Mister-Industries/tinyCore/assets/Photos/image2.png

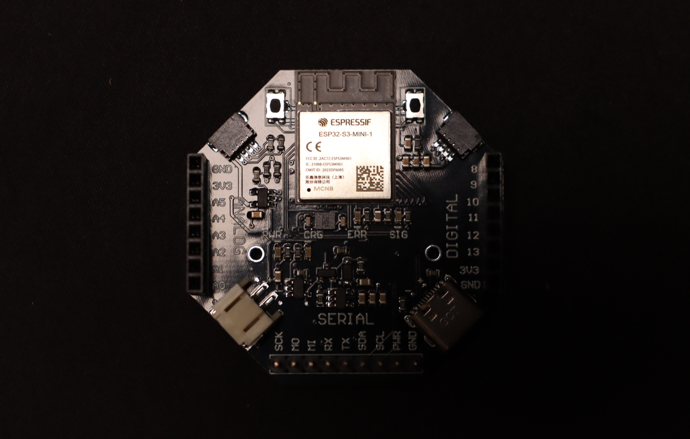
assets/Photos/image2.png
