Mister-Industries/tinyCore/assets/Photos/image5.png

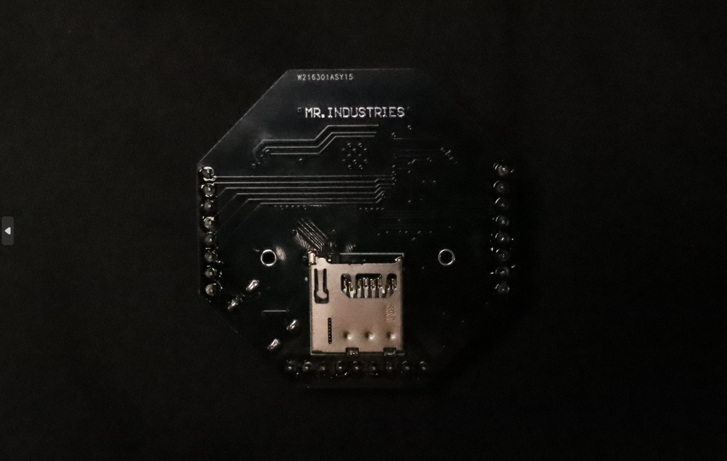
assets/Photos/image5.png
