Mister-Industries/tinyCore/assets/Photos/image6.png

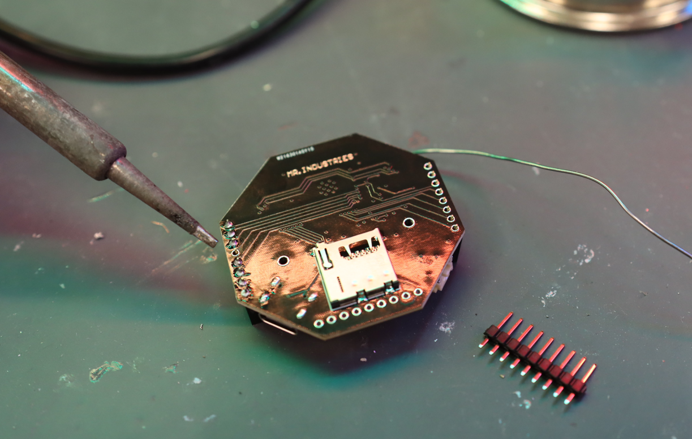
assets/Photos/image6.png
