Mister-Industries/tinyCore/assets/Photos/image7.png

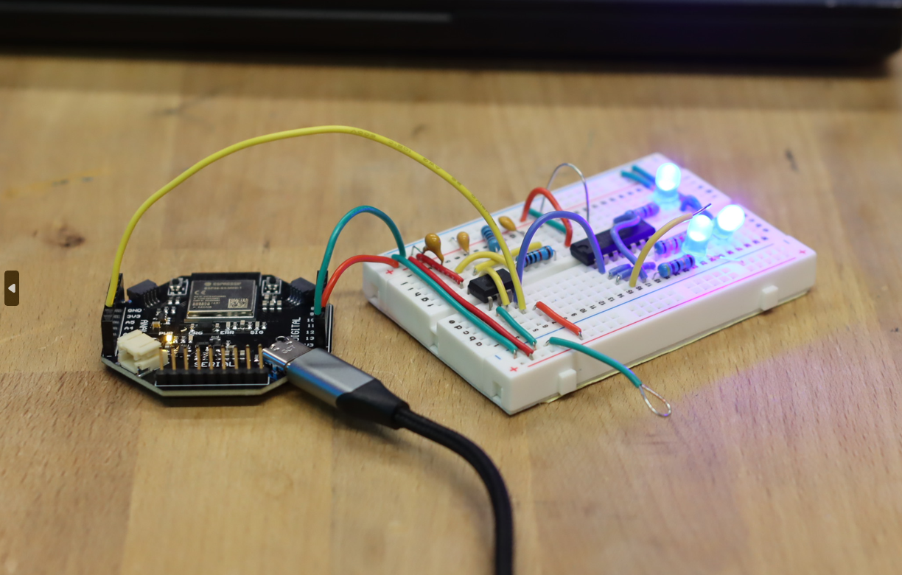
assets/Photos/image7.png
