Mister-Industries/tinyCore/assets/Photos/image9.png

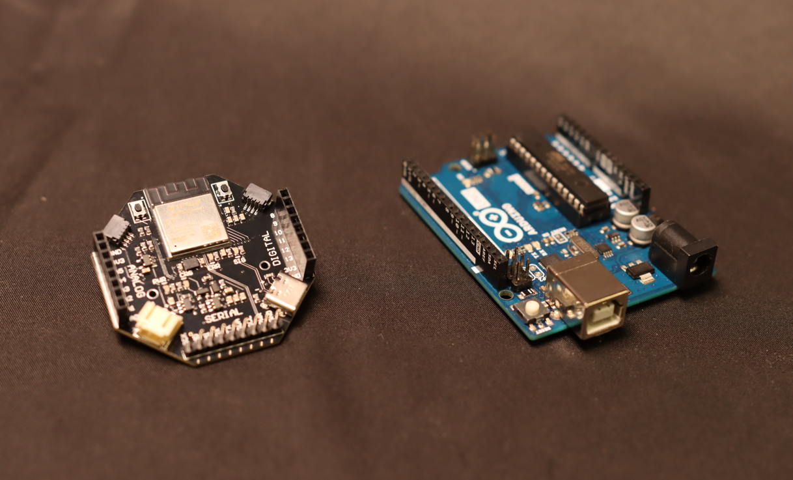
assets/Photos/image9.png
