Mister-Industries/tinyCore/assets/Photos/tinyCore-4Colors.png

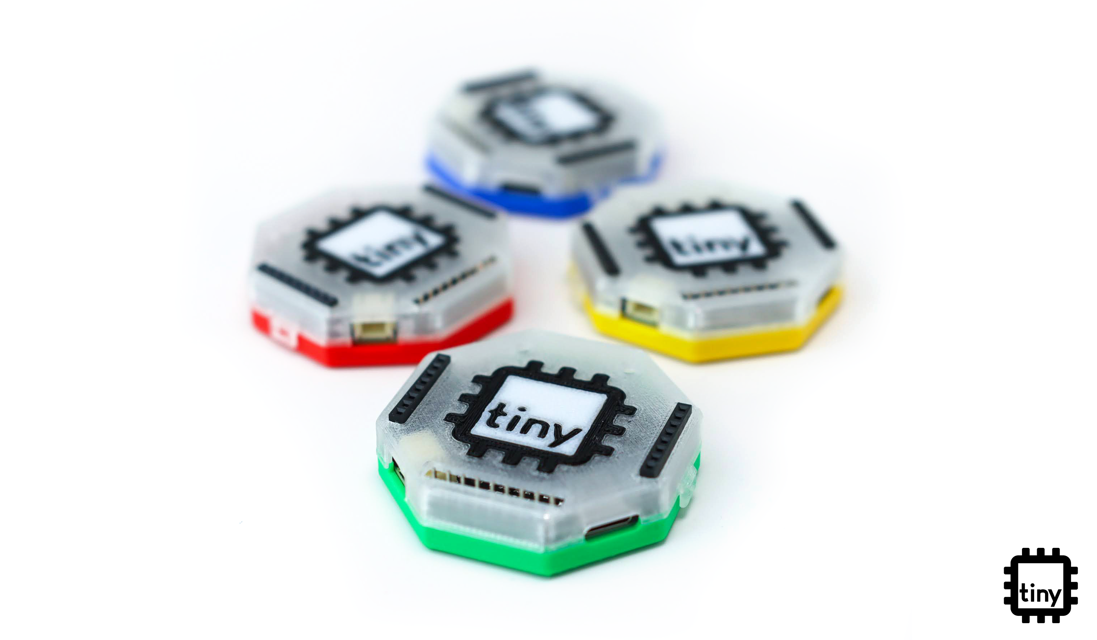
assets/Photos/tinyCore-4Colors.png
