Mister-Industries/tinyCore/assets/Photos/tinyCore-store-2.jpg

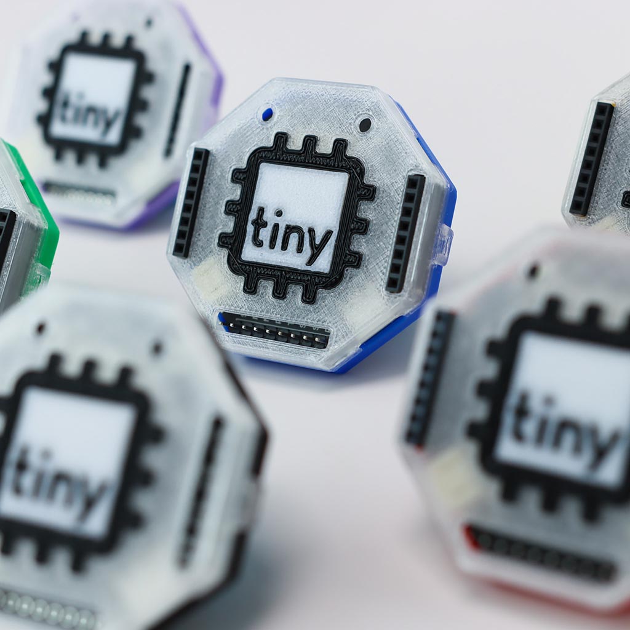
assets/Photos/tinyCore-store-2.jpg
