Mister-Industries/tinyCore/assets/Photos/tinyCore-store-3.jpg

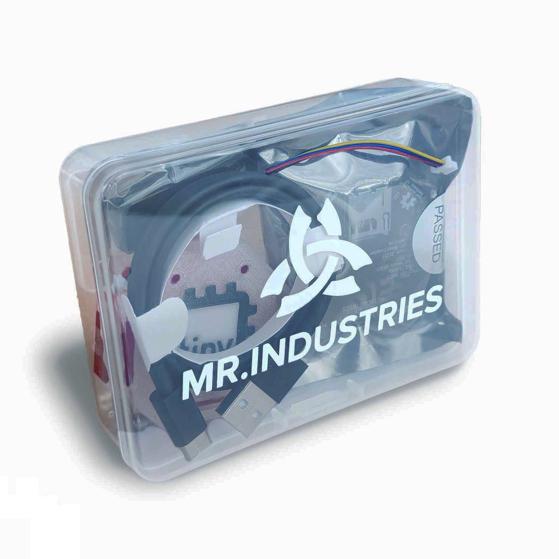
assets/Photos/tinyCore-store-3.jpg
