Mister-Industries/tinyCore/assets/Photos/tinyCore-store-3.png

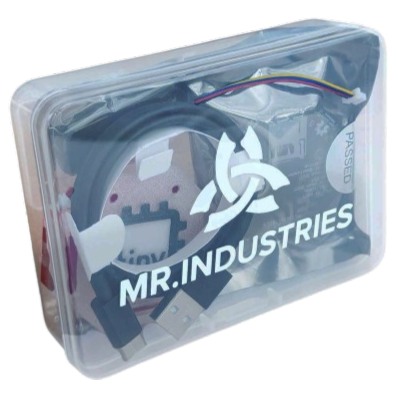
assets/Photos/tinyCore-store-3.png
