Mister-Industries/tinyCore/assets/Photos/tinyCore-store-4.jpg

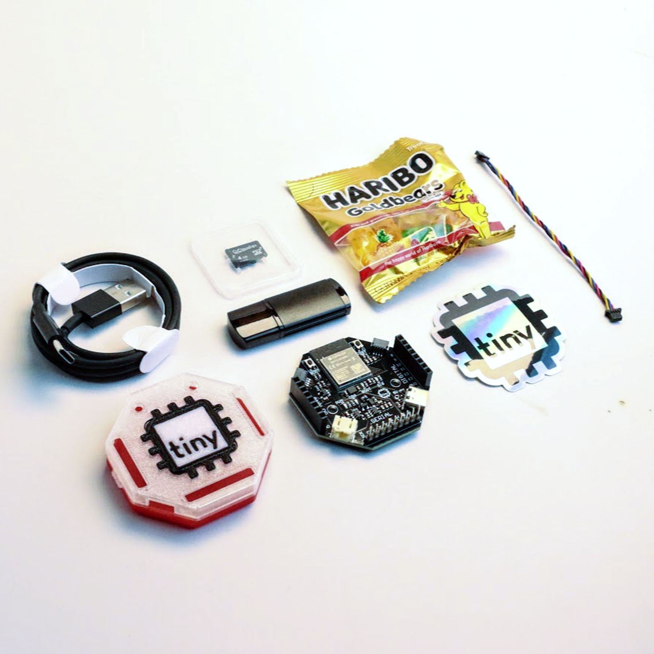
assets/Photos/tinyCore-store-4.jpg
