Mister-Industries/tinyCore/assets/Photos/tinyCore-store-5.jpg

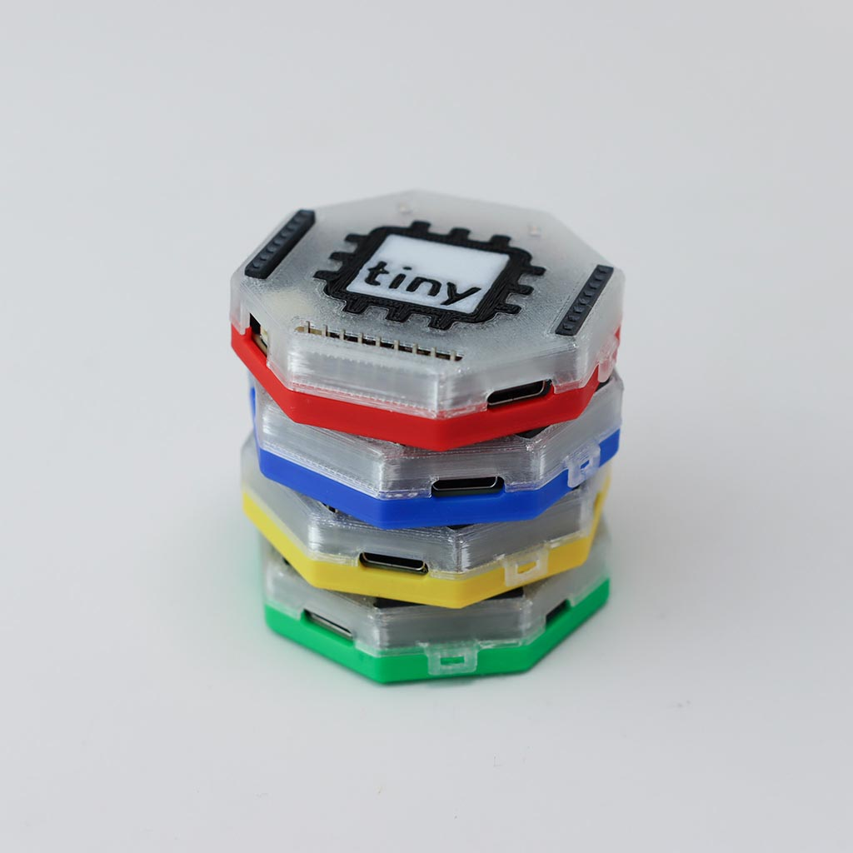
assets/Photos/tinyCore-store-5.jpg
