Mister-Industries/tinyCore/assets/Renders/Backside.png

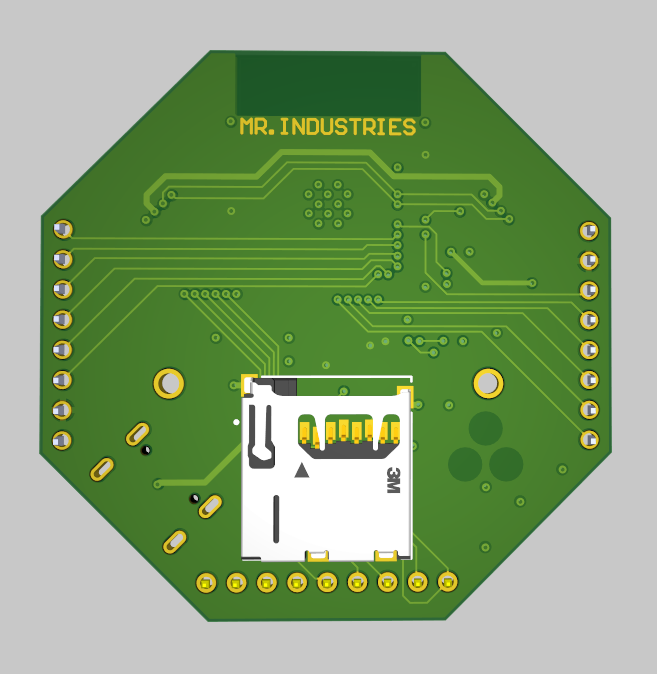
assets/Renders/Backside.png
