Mister-Industries/tinyCore/assets/Renders/IotaCoreRender.png

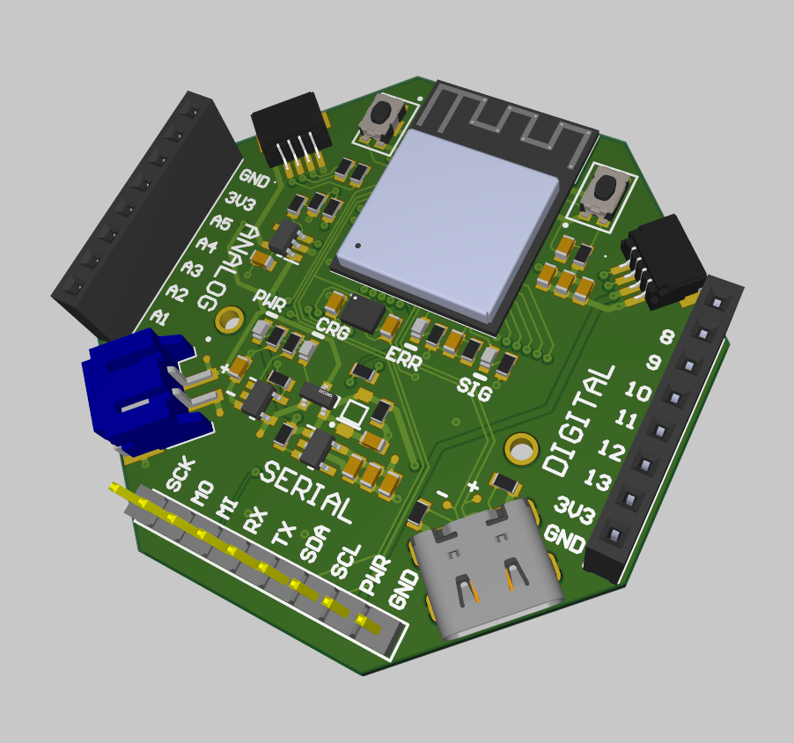
assets/Renders/IotaCoreRender.png
