Mister-Industries/tinyCore/Software/Arduino/Examples/ESP-NOW/ESP_NOW_Serial_AP/ESP_NOW_Serial_AP.ino

/*
    ESP-NOW Serial Example - Unicast transmission
    Lucas Saavedra Vaz - 2024
    Send data between two ESP32s using the ESP-NOW protocol in one-to-one (unicast) configuration.
    Note that different MAC addresses are used for different interfaces.
    The devices can be in different modes (AP or Station) and still communicate using ESP-NOW.
    The only requirement is that the devices are on the same Wi-Fi channel.
    Set the peer MAC address according to the device that will receive the data.

    Example setup:
    - Device 1: AP mode with MAC address F6:12:FA:42:B6:E8
                Peer MAC address set to the Station MAC address of Device 2 (F4:12:FA:40:64:4C)
    - Device 2: Station mode with MAC address F4:12:FA:40:64:4C
                Peer MAC address set to the AP MAC address of Device 1 (F6:12:FA:42:B6:E8)

    The device running this sketch will also receive and print data from any device that has its MAC address set as the peer MAC address.
    To properly visualize the data being sent, set the line ending in the Serial Monitor to "Both NL & CR".
*/

#include "ESP32_NOW_Serial.h"
#include "MacAddress.h"
#include "WiFi.h"

#include "esp_wifi.h"

// 0: AP mode, 1: Station mode
#define ESPNOW_WIFI_MODE_STATION 0

// Channel to be used by the ESP-NOW protocol
#define ESPNOW_WIFI_CHANNEL 1

#if ESPNOW_WIFI_MODE_STATION          // ESP-NOW using WiFi Station mode
#define ESPNOW_WIFI_MODE WIFI_STA     // WiFi Mode
#define ESPNOW_WIFI_IF   WIFI_IF_STA  // WiFi Interface
#else                                 // ESP-NOW using WiFi AP mode
#define ESPNOW_WIFI_MODE WIFI_AP      // WiFi Mode
#define ESPNOW_WIFI_IF   WIFI_IF_AP   // WiFi Interface
#endif

// Set the MAC address of the device that will receive the data
// For example: F4:12:FA:40:64:4C
const MacAddress peer_mac({0xF0, 0xF5, 0xBD, 0x50, 0xB0, 0x80});

ESP_NOW_Serial_Class NowSerial(peer_mac, ESPNOW_WIFI_CHANNEL, ESPNOW_WIFI_IF);

void setup() {
  Serial.begin(115200);

  Serial.print("WiFi Mode: ");
  Serial.println(ESPNOW_WIFI_MODE == WIFI_AP ? "AP" : "Station");
  WiFi.mode(ESPNOW_WIFI_MODE);

  Serial.print("Channel: ");
  Serial.println(ESPNOW_WIFI_CHANNEL);
  WiFi.setChannel(ESPNOW_WIFI_CHANNEL, WIFI_SECOND_CHAN_NONE);

  while (!(WiFi.STA.started() || WiFi.AP.started())) {
    delay(100);
  }

  Serial.print("MAC Address: ");
  Serial.println(ESPNOW_WIFI_MODE == WIFI_AP ? WiFi.softAPmacAddress() : WiFi.macAddress());

  // Start the ESP-NOW communication
  Serial.println("ESP-NOW communication starting...");
  NowSerial.begin(115200);
  Serial.println("You can now send data to the peer device using the Serial Monitor.\n");

  Serial.println("Commands:");
  Serial.println("'s' - Start IMU data transmission");
  Serial.println("'t' - Run throughput test");
  Serial.println("'x' - Stop current operation");
}

void loop() {
  while (NowSerial.available()) {
    Serial.write(NowSerial.read());
  }

  while (Serial.available() && NowSerial.availableForWrite()) {
    if (NowSerial.write(Serial.read()) <= 0) {
      Serial.println("Failed to send data");
      break;
    }
  }

  delay(1);
}
